ADElectronics/RTL00_WEB_WS2812/Device body/Top.SLDPRT

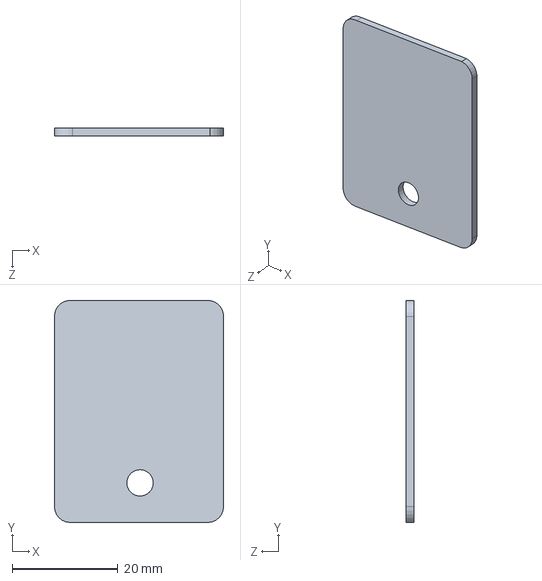
[picture p5: CAD file, 2017-12-26]
Device body/Top.SLDPRT
32.0 x 42.0 x 1.50 mm
