ADElectronics/RTL00_WEB_WS2812/Device body/Base.SLDPRT

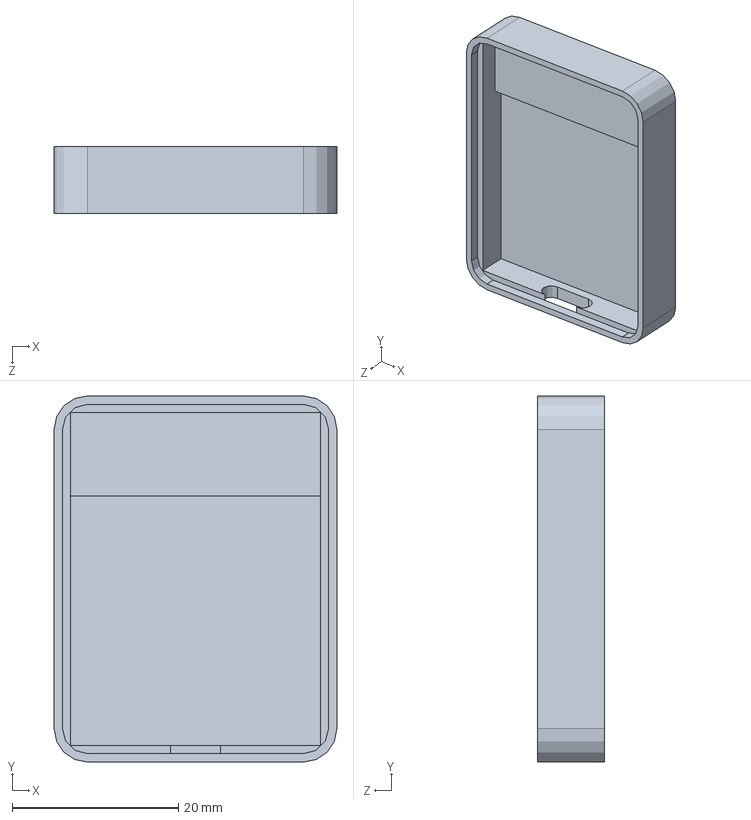
[picture p6: CAD file, 2017-12-26]
Device body/Base.SLDPRT
34.0 x 44.0 x 8.00 mm
