ADElectronics/RTL00_WEB_WS2812/Device body/Button.SLDPRT

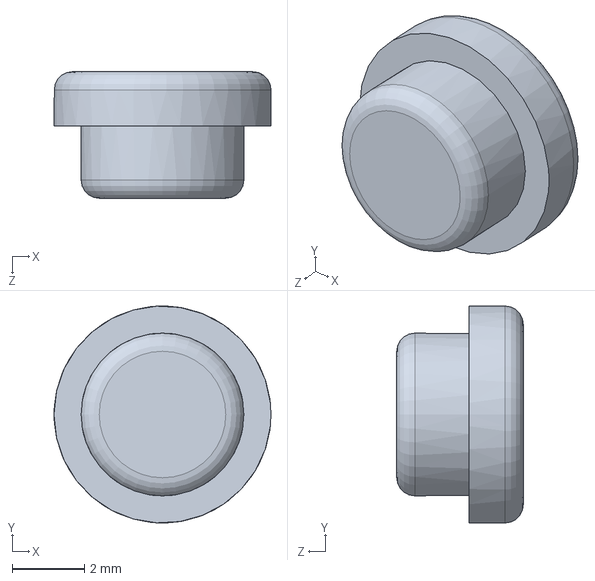
[picture p7: CAD file, 2017-12-26]
Device body/Button.SLDPRT
6.00 x 6.00 x 3.50 mm
