ADElectronics/RTL00_WEB_WS2812/Firmware/Project/build_info.h

#define UTS_VERSION "2018/01/29-16:33:25"
#define RTL8195AFW_COMPILE_TIME "2018/01/29-16:33:26"
#define RTL8195AFW_COMPILE_DATE "20180129"
#define RTL8195AFW_COMPILE_BY "Andrew"
#define RTL8195AFW_COMPILE_HOST ""
#define RTL8195AFW_COMPILE_DOMAIN
#define RTL195AFW_COMPILER "gcc 6.3.1"
