ADElectronics/RTL00_WEB_WS2812/Firmware/Project/user_start.c

/*
 * user_start.c
 *
 *  Created on: 26/03/2017
 *      Author: pvvx
 */
#include "user_config.h"
#include "platform_autoconf.h"
#include "autoconf.h"
#include "FreeRTOS.h"
#include "freertos_pmu.h"
#include "tcm_heap.h"
#include "task.h"
#include "diag.h"
#include "netbios/netbios.h"
#include "sntp/sntp.h"
#include "sys_cfg.h"
#include "wifi_api.h"
#include "web/web_srv.h"
#include "webfs/webfs.h"

// mbed
#include "gpio_api.h" 
#include "i2c_api.h"
#include "pinmap.h"

// User
#include "ledeffectsserver.h"

#include "lwip/pbuf.h"
#include "lwip/udp.h"
#include "lwip/tcp.h"

struct SystemCfg syscfg = {
		.cfg.w = SYS_CFG_DEBUG_ENA
		 | SYS_CFG_PIN_CLR_ENA
#if defined(USE_NETBIOS) && USE_NETBIOS
		 | SYS_CFG_NETBIOS_ENA
#endif
#if defined(USE_SNTP) && USE_SNTP
		 | SYS_CFG_SNTP_ENA
#endif
		 ,
#if defined(USE_WEB)
		.web_port = USE_WEB,
#else
		.web_port = 0,
#endif
		.web_twrec = 5,
		.web_twcls = 5
};

SemaphoreHandle_t sema_WEBReady = NULL;

extern void ShowMemInfo(void);
void connect_start(void)
{
	info_printf("\%s: Time at start %d ms.\n", __func__, xTaskGetTickCount());
}

void connect_close(void)
{
	info_printf("\%s: Time at start %d ms.\n", __func__, xTaskGetTickCount());
}

void user_start(void)
{
	info_printf("\%s: Time at start %d ms.\n", __func__, xTaskGetTickCount());

}

void sys_write_cfg(void)
{
	flash_write_cfg(&syscfg, FEEP_ID_SYS_CFG, sizeof(syscfg));
}

extern void console_init(void);

void user_ws_thrd(void)
{
	ledEffectsServer_Init();

	while (1)
	{
		if (xSemaphoreTake(sema_WEBReady, 10 * configTICK_RATE_HZ))
		{
			ledEffectsServer_Task();
		}
		WDGRefresh();
	}
}

void user_init_thrd(void) 
{
	sema_WEBReady = xSemaphoreCreateMutex();
	if (xSemaphoreTake(sema_WEBReady, configTICK_RATE_HZ))
	{
		/*
		if(syscfg.cfg.b.pin_clear_cfg_enable && 0)
		{
			// user_test_clear_pin();
			wifi_cfg.load_flg = 0;
		}
		else flash_read_cfg(&syscfg, FEEP_ID_SYS_CFG, sizeof(syscfg));
		*/
		wifi_cfg.load_flg = 0;

		if (!syscfg.cfg.b.debug_print_enable) print_off = 1;

		//console_init();
		WEBFSInit();
		wifi_init(); // Load cfg, init WiFi + LwIP init, WiFi start if wifi_cfg.mode !=  RTW_MODE_NONE 

#if defined(USE_NETBIOS)
		if (syscfg.cfg.b.netbios_ena) netbios_init();
#endif
#if defined(USE_SNTP)
		if (syscfg.cfg.b.sntp_ena) sntp_init();
#endif

		webserver_init(syscfg.web_port);

		if (syscfg.cfg.b.powersave_enable)
		{
			release_wakelock(~WAKELOCK_WLAN);
		}

		xSemaphoreGive(sema_WEBReady);
	}
	ShowMemInfo();
	vTaskDelete(NULL);
}
